ZoeGet/CodexLigt/Firmware/include/wifi_secrets.example.h

#ifndef CODEXLIGHT_WIFI_SECRETS_H
#define CODEXLIGHT_WIFI_SECRETS_H

// Copy this file to wifi_secrets.h and fill in your Wi-Fi credentials.
// wifi_secrets.h is ignored by Git.
// The UDP control token is paired at runtime and stored in ESP32 NVS,
// so it does not need to be written here.

#define CODEXLIGHT_WIFI_SSID "YourWiFiName"
#define CODEXLIGHT_WIFI_PASSWORD "YourWiFiPassword"

#endif  // CODEXLIGHT_WIFI_SECRETS_H
